bvksound/UPL-B1/Documentation/Connections.png

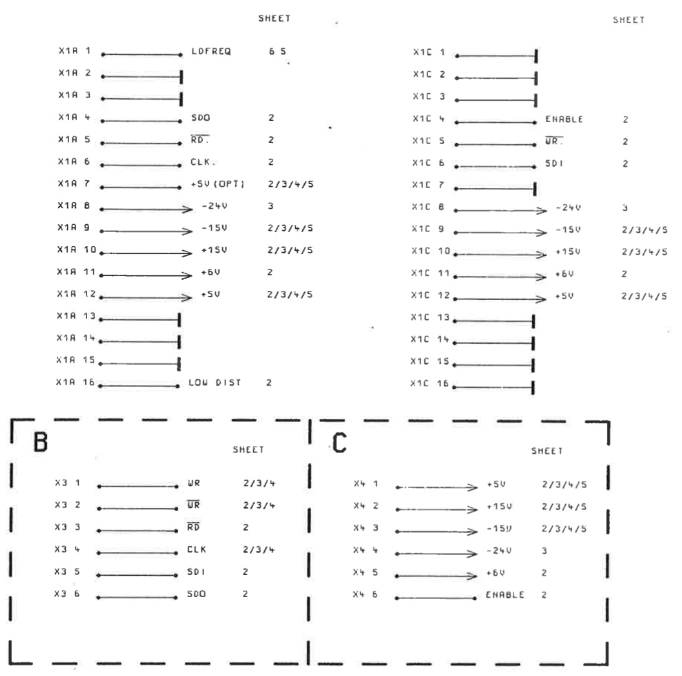
Documentation/Connections.png
