bvksound/UPL-B1/Photo's/29E0DB71-026A-44F6-90F2-016BDC316CC1_1_105_c.jpeg

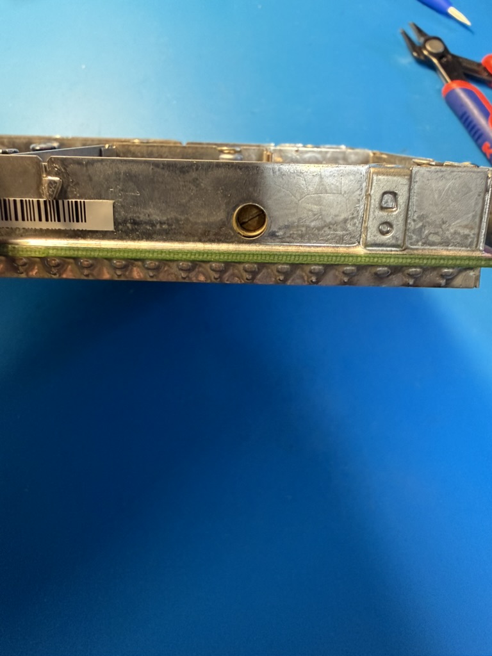
Photo's/29E0DB71-026A-44F6-90F2-016BDC316CC1_1_105_c.jpeg
