bvksound/UPL-B1/Photo's/95BCCA6E-4D61-4A19-A952-14102BD93FDB_1_105_c.jpeg

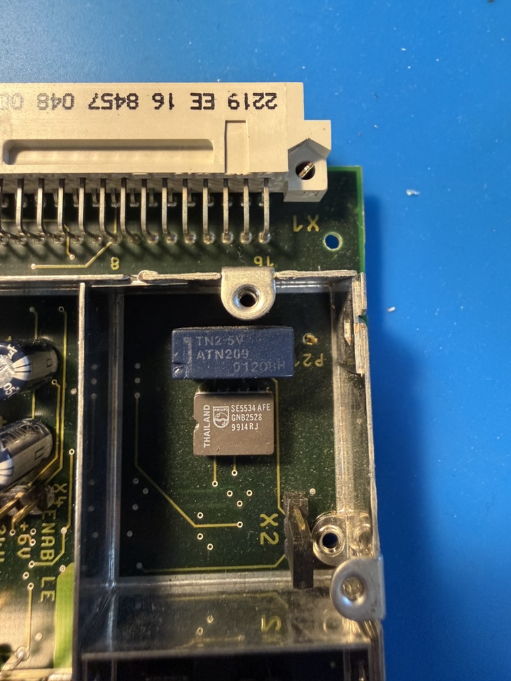
Photo's/95BCCA6E-4D61-4A19-A952-14102BD93FDB_1_105_c.jpeg
