bvksound/UPL-B1/Photo's/439F39ED-26D9-4540-9994-5D5942BE2B61_1_105_c.jpeg

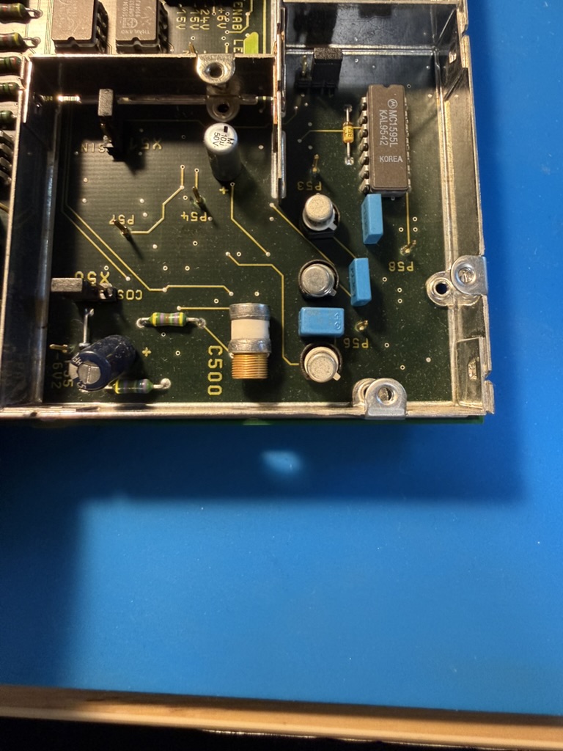
Photo's/439F39ED-26D9-4540-9994-5D5942BE2B61_1_105_c.jpeg
