bvksound/UPL-B1/Photo's/935FF496-B8E4-4063-B757-0149B8D1954E_1_105_c.jpeg

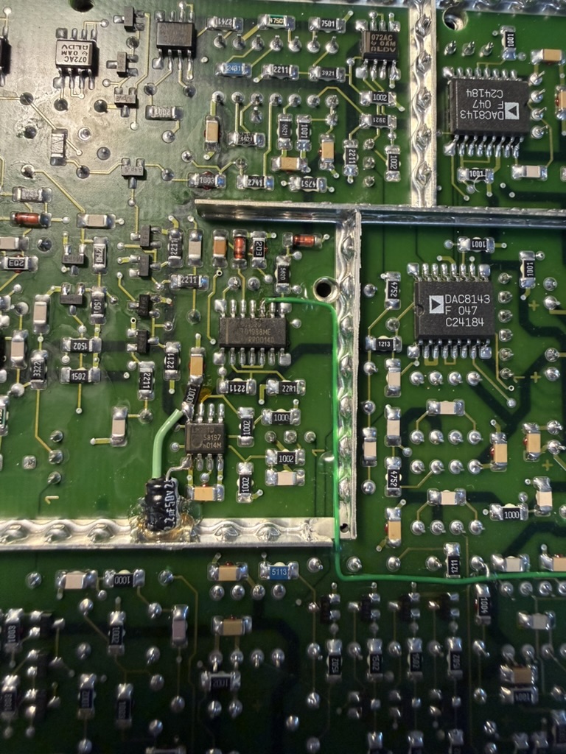
Photo's/935FF496-B8E4-4063-B757-0149B8D1954E_1_105_c.jpeg
