bvksound/UPL-B1/Photo's/A2E01441-EE9E-403F-8A4C-0F25788E6186_1_105_c.jpeg

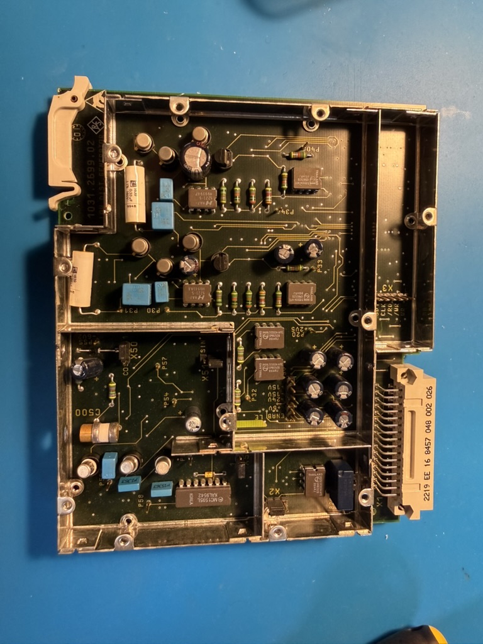
Photo's/A2E01441-EE9E-403F-8A4C-0F25788E6186_1_105_c.jpeg
