bvksound/UPL-B1/Photo's/F87B208C-721B-489F-BFD8-CCA708AC9017_1_105_c.jpeg

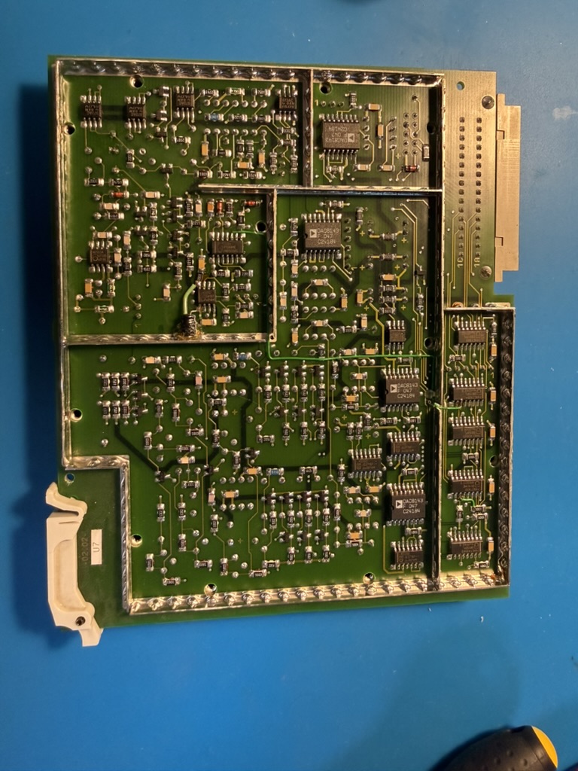
Photo's/F87B208C-721B-489F-BFD8-CCA708AC9017_1_105_c.jpeg
